hkueller/IoT_Anzeiger_V2/Network.cc

#include <Network.h>

network::network() {
	void *ptr;
	ptr=(WiFiServer *) malloc(sizeof(WiFiServer));
	server = (WiFiServer *) new(ptr) WiFiServer(80);
	ptr=(PubSubClient *) malloc(sizeof(PubSubClient));
	mqtt = (PubSubClient *) new(ptr) PubSubClient(mqtt_client);
}

void network::begin() {
	int retry=200;
	int zahl=0;
	clientId = "display_";

	//wifimanager.resetSettings();
	wifimanager.setConfigPortalTimeout(300);
#ifdef DEBUG
	Serial.println("Connecting WLAN");
	Serial.flush();
#endif
	if( ! wifimanager.autoConnect("IOTAnzeiger") ) {
#ifdef DEBUG
		Serial.println("Connecting to WLAN failed");
		Serial.println("Resetting the device");
		Serial.flush();
#endif
		ESP.restart();
	}
	ArduinoOTA.onStart([]() {
		String type;
		if (ArduinoOTA.getCommand() == U_FLASH) {
			type = "sketch";
		} else { // U_FS
			type = "filesystem";
		}
	});
#ifdef DEBUG
	Serial.println("Trying to get time from network");
	Serial.flush();
#endif
	configTime(MY_TZ, MY_NTP_SERVER);
	while(!getLocalTime(&zeit)) {
		if ( zahl < retry ) {
#ifdef DEBUG
			Serial.println("Time still not available. retry: " + String(zahl));
			Serial.flush();
#endif
			delay(100);
			zahl++;
		} else {
#ifdef DEBUG
			Serial.println("Timesetup failed");
			Serial.flush();
#endif
			break;
		}

	}
#ifdef DEBUG
	Serial.println("Initializing OTA");
	Serial.flush();
#endif
  	ArduinoOTA.begin();
#ifdef DEBUG
	Serial.println("Initializing WEB Server");
	Serial.flush();
#endif
	server->begin();
	server->setNoDelay(true);
#ifdef DEBUG
	Serial.println("Initializing MQTT Service");
	Serial.flush();
#endif
	mqtt->setServer(MQTT_SERVER,MQTT_PORT);
	mqtt->setCallback(mqtt_cb);
	clientId += String(random(0xffff), HEX);
#ifdef DEBUG
	Serial.print("Attempting MQTT connection...");
	Serial.flush();
#endif
	if (mqtt->connect(clientId.c_str())) {
#ifdef DEBUG
		Serial.print("connected, sending false to ");
		Serial.println(MQTT_REQUEST_TOPIC);
		Serial.flush();
#endif
		// Once connected, publish an announcement...
		mqtt->publish(MQTT_REQUEST_TOPIC, "false");
		// ... and resubscribe
#ifdef DEBUG
		Serial.print("subscribe ");
		Serial.println(MQTT_SUBSCRIBE_TOPIC);
		Serial.flush();
#endif
		mqtt->subscribe(MQTT_SUBSCRIBE_TOPIC);
#ifdef DEBUG
		Serial.println("mqtt setup ready");
		Serial.flush();
#endif
	}
#ifdef DEBUG
	Serial.println("Connecting to FHEM Instance");
	Serial.flush();
#endif
	network::FhemConnect();
	yield();
#ifdef DEBUG
	Serial.println("NETWORK SETUP FINISHED");
	Serial.flush();
#endif
	lastconfig=millis() + 1000*60;
}

int network::testNet(display *disp, smarthome *config) {
	int rc=0;
	int wifi_retry = 0;
	String reconmes="";
/*#ifdef DEBUG
	Serial.println("testNet() running");
	Serial.println("checking if WiFi is still connected");
	Serial.flush();
#endif*/
	while(WiFi.status() != WL_CONNECTED && wifi_retry < 15 ) {
#ifdef DEBUG
		Serial.println("Network Offline, Reconnect");
        	Serial.flush();
#endif
		reconmes="Try to Reconnect: ";
		reconmes+=wifi_retry;
		disp->Message("Network Offline!", reconmes, config);
		WiFi.disconnect();
		delay(100);
		wifimanager.setConfigPortalTimeout(300);
		wifimanager.autoConnect("IOTAnzeiger");
		delay(100);
		wifi_retry++;
		rc=1;
	}
	if(WiFi.status() != WL_CONNECTED) {
#ifdef DEBUG
		Serial.println("Network Offline, Reconnect failed, forcing system reset");
        	Serial.flush();
#endif
		disp->Message("Network Offline", "Rebooting", config);
		ESP.restart();
	}
	if((WiFi.status() == WL_CONNECTED) && ( rc == 1) ) {
		disp->Message("Network Reconnected","Setting up Network Services", config);
#ifdef DEBUG
		Serial.println("Cleaning up FhemConnection");
		Serial.flush();
#endif
		if(fhemclient) {
			FhemDisconnect();
		}
#ifdef DEBUG
		Serial.println("Checking for OTA");
        	Serial.flush();
#endif
  		ArduinoOTA.begin();
#ifdef DEBUG
		Serial.println("Pull System time with ntp");
        	Serial.flush();
#endif
		configTime(MY_TZ, MY_NTP_SERVER);
#ifdef DEBUG
		Serial.println("starting the servers");
        	Serial.flush();
#endif
		server->begin();
		server->setNoDelay(true);
		if (mqtt->connect(clientId.c_str())) {
#ifdef DEBUG
			Serial.print("connected, sending false to ");
			Serial.println(MQTT_REQUEST_TOPIC);
			Serial.flush();
#endif
			// Once connected, publish an announcement...
			mqtt->publish(MQTT_REQUEST_TOPIC, "false");
			// ... and resubscribe
#ifdef DEBUG
			Serial.print("subscribe ");
			Serial.println(MQTT_SUBSCRIBE_TOPIC);
			Serial.flush();
#endif
			mqtt->subscribe(MQTT_SUBSCRIBE_TOPIC);
#ifdef DEBUG
			Serial.println("mqtt setup ready");
			Serial.flush();
#endif
		}
		network::FhemConnect();
		network::mqttConnect();
		yield();
	}
	return(rc);
}

void network::handleWeb(smarthome *data) {
	//some variables
	//here for the actual client connection
	WiFiClient webclient;
	//and a buffer used to build the 
	//buffer to store the data send bei the client

	//Let us show if some client 
	//is available
	webclient = server->accept();
	if (webclient) {
		//do this only if we have a client
		String currentline = "";
		while(webclient.connected()) {
			//and if the client connection was successfull
			if (webclient.available()) {
				//and the client is still there
				//first of all we must take the initial GET call
				//of the client anywhere (http protocoll definition)
				//so let us read the send string char by char
				char c = webclient.read();
				header +=c;
				if ( c == '\n' ) {
					//OK we recived the newline command
					if (currentline.length() == 0 ) {
						//and nothing else - it was just a 
						//empty line -> we are ready to send our data

						//define a string to convert our
						//float values to stings
						String temp;
						//Let us load the web page into the temp string
						//start with HTML Header Information
						temp="HTTP/1.1 200 OK\n";
						temp+="Content-type:text/html\n";
						temp+="Connection: close\n\n";
						temp+="<!DOCTYPE HTML PUBLIC \"-//W3C//DTD HTML 4.0 Transitional//EN\">\n";
						temp+="<html><head><meta http-equiv=\"refresh\" content=\"60\"></head><body>\n";
						//stylesheed for a better table display
						temp+="<style>\ntable {\nborder-collapse: seperate;\nborder-spacing: 0.2em;\n}\ntbody tr:nth-child(even) td {\nbackground-color: #e4ebf2;\ncolor: #000;\n}\n\n";
						temp+="</style>\n\n";
						//start with the HTML HEader Information
						//display a Head Line and add some empty lines
						temp+="<H1><center>IOT Display Device</center>\n";
						temp+="</H1><br><br><center><table border=0 cellpadding=\"8\" cellspacing=\"0\" width=\"80%\"><tbody>\n";
						//get the information for the last data update
						temp+="<tr><td>Last Update:</td><td style=\"text-align:right\">\n";
						temp+=twodigit(zeit.tm_mday);
						temp+=".";
						temp+=twodigit(zeit.tm_mon+1);
						temp+=".";
						temp+=zeit.tm_year+1900;
						temp+=" ";
						temp+=twodigit(zeit.tm_hour);
						temp+=":";
						temp+=twodigit(zeit.tm_min);
						temp+=".";
						temp+=twodigit(zeit.tm_sec);
						if(data->SetFirst()) {
							if ( ! data->IsHeadline() ) {
								temp+="</td></tr><tr><td>";
								temp+=data->GetName();
								temp+=":</td><td style=\"text-align:right\">\n";
								temp+=data->GetData();
							}
							while(data->SetNext()) {
								if ( ! data->IsHeadline() ) {
									temp+="</td></tr><tr><td>";
									temp+=data->GetName();
									temp+=":</td><td style=\"text-align:right\">\n";
									temp+=data->GetData();
									temp+=" ";
									temp+=data->GetEinheit();
								}
							}
						}
						temp+="</td></tr></tbody></table></center><br></body></html>\n\n";
						//now send the string buffer
						webclient.print(temp);
						//and jump out -> we are ready and will close the connection
						break;
					} else {
						//this was not a empty line - so we have still to get data
						//empty the variable, and startover for the next line
						currentline = "";
					}
				} else if ( c != '\r' ) {
					//collect the line send by client char for char.
					currentline += c;
				}
			}
		}
		//reset our header variable
		header = "";
		// and stop the client connection
		webclient.flush();
		webclient.stop();
	}
	//give ESP8266 time to to wlan stuff
	yield();
}


int network::FhemConnect() {
	int conntry=0;

	if ( !fhemclient ) {
		void *ptr;
		ptr=(WiFiClient *) malloc(sizeof(WiFiClient));
		fhemclient = (WiFiClient *) new(ptr) WiFiClient();
		if(!fhemclient) {
			return 1;
		}
	}

	while ( ! fhemclient->connected() ) {
		if (!fhemclient->connect(FHEM_HOST, FHEM_PORT)) {
			yield();
			delay(100);
		}
		conntry++;
		if(conntry > 10) {
			return 1;
		}
	}
	return 0;
}

void network::FhemDisconnect() {
	if(fhemclient) {
		fhemclient->flush();
		fhemclient->stop();
		delete(fhemclient);
		fhemclient=0;
	}
}

int network::FhemConnCheck() {
	int connectry=0;
	while( FhemConnect() == 1 ) {
#ifdef DEBUG
		Serial.println("Try to reconnect FHEM");
#endif
		if(connectry > 10 ) {
			break;
		}
		yield();
		delay(100);
		connectry++;
		if (connectry > 10) {
			return 1;
		}
	}
	return 0;
}

void network::UpdateData(display *disp, smarthome *data) {
	String Result;

	if(FhemConnCheck() == 1) { return; };
#ifdef DEBUG
	Serial.println("FHEM Connection OK\n");
        Serial.flush();
        Serial.flush();
#endif
	fhemclient->print("\n");
	while(fhemclient->available()) {
		Result = fhemclient->readStringUntil('\n');
	}
	fhemclient->flush();
#ifdef DEBUG
	Serial.println("Start reading data");
        Serial.flush();
#endif
	if(data->SetFirst()) {
		if ( ! data->IsHeadline() ) {
			for ( int i=0; i<FHEM_RETRY; i++) {
#ifdef DEBUG
				Serial.println(data->GetDev() + "->" + data->GetReading() );
				Serial.flush();
#endif
				if(FhemConnCheck() == 1) { return; };
				if (FhemGetData(&Result, data->GetDev(), data->GetReading()) == 1 ) {
					data->SetData(Result);
					break;
				} else {
					Result="-1";
					data->SetData(Result);
				}
			}
		}
		while(data->SetNext()) {
			for ( int i=0; i<FHEM_RETRY; i++) {
#ifdef DEBUG
				Serial.println(data->GetDev() + "->" + data->GetReading() );
				Serial.flush();
#endif
				if(FhemConnCheck() == 1) { return; };
				if (FhemGetData(&Result, data->GetDev(), data->GetReading()) == 1 ) {
					data->SetData(Result);
					break;
				} else {
					Result="-1";
					data->SetData(Result);
				}
			}
		}
#ifdef DEBUG
		Serial.println("Updateing Timer");
        	Serial.flush();
#endif
		StoreTimeLastRead();
		Result=twodigit(zeit.tm_mday);
		Result+=".";
		Result+=twodigit(zeit.tm_mon+1);
		Result+=" ";
		Result+=twodigit(zeit.tm_hour);
		Result+=":";
		Result+=twodigit(zeit.tm_min);
		disp->SetDate(Result);
		disp->EnableUpdate();
		/*
#ifdef DEBUG
		Serial.println("Clearing fhem read buffer");
        	Serial.flush();
#endif
		while(fhemclient->available()) {
			fhemclient->flush();
			yield();
		}*/
#ifdef DEBUG
		Serial.println("quitting fhem");
        	Serial.flush();
#endif
		fhemclient->print("quit\n");
	} else {
		RequestConfig();
		fhemclient->print("quit\n");
	}
#ifdef DEBUG
	Serial.println("Reading data completed");
	Serial.flush();
#endif
};

int network::FhemGetData(String *result, const String device, const String reading) {
	String buffer;
	int pos;
	int readwait=0;

	*result="";
#ifdef DEBUG
	Serial.println("Flushing Network input");
       	Serial.flush();
#endif
	while(fhemclient->available()) {
		buffer = fhemclient->read();
	}
	buffer = "{ ReadingsVal(\"" + device + "\",\"" + reading + "\",0) }\n";
#ifdef DEBUG
	Serial.println("Send fhem command");
       	Serial.flush();
#endif
	fhemclient->print(buffer);
#ifdef DEBUG
	Serial.println("Waiting for answer");
       	Serial.flush();
#endif
	readwait=0;
	while(fhemclient->available() < 1 ) {
		yield();
		delay(100);
		readwait++;
		if ( readwait > 50 ) {
			break;
		}
	}
#ifdef DEBUG
	Serial.println("Reading answer");
       	Serial.flush();
#endif
	*result=fhemclient->readStringUntil('\n');
	result->trim();
	pos=result->indexOf("fhem>");
	if(pos > -1) {
		*result=result->substring(pos+5);
	}
#ifdef DEBUG
	Serial.println("done");
       	Serial.flush();
#endif
	return(1);
}

void network::handleOTA() {
	ArduinoOTA.handle();
}

void network::handleNet(smarthome *sm, display *disp) {
/*#ifdef DEBUG
	Serial.println("Running mqtt loop");
	Serial.flush();
#endif*/
	if(mqtt->connected()) {
		mqtt->loop();
	} else {
		network::mqttConnect();
	}
	yield();
/*#ifdef DEBUG
	Serial.println("Running OTA");
	Serial.flush();
#endif*/
	ArduinoOTA.handle();
	yield();
	if ( millis() - disp->getLastTime() > UPDATE_MINUTE * 1000 * 60) {
#ifdef DEBUG
		Serial.println("Updating smarthome Data");
		Serial.flush();
#endif
		UpdateData(disp,sm);
		yield();
	}
/*#ifdef DEBUG
	Serial.println("Running WEB");
#endif*/
	handleWeb(sm);
	yield();
/*#ifdef DEBUG
	Serial.print("millies: ");
	Serial.print(millis());
	Serial.print(" lasttime: ");
	Serial.println(lastconfig);
#endif*/
	if ( millis() > (lastconfig + (1000*600)) ) {
#ifdef DEBUG
		Serial.println("Requesting Config");
#endif
		RequestConfig();
		lastconfig=millis();
	}
}

void network::StoreTimeLastRead() {
        time_t now;

        now = time(nullptr);
        localtime_r(&now, &zeit);
}

int network::ReturnYear() {
	return(zeit.tm_year+1990);
}

int network::ReturnMonth() {
	return(zeit.tm_mon);
}

int network::ReturnDay() {
	return(zeit.tm_mday);
}

int network::ReturnHour() {
	return(zeit.tm_hour);
}

int network::ReturnMinutes() {
	return(zeit.tm_min);
}

String network::ReturnSeconds() {
	String seconds;

	if ( zeit.tm_sec < 0 ) {
		seconds=0;
		seconds+=zeit.tm_sec;
	} else {
		seconds=zeit.tm_sec;
	}
	return(seconds);
}

String network::twodigit(int number) {
	String buffer;

	buffer="";
	if ( number < 10 ) {
		buffer+="0";
	}
	buffer+=number;
	return(buffer);
}

void network::RequestConfig() {
	mqtt->publish(MQTT_REQUEST_TOPIC,"true");
}

void network::ConfigDone() {
	mqtt->publish(MQTT_REQUEST_TOPIC,"false");
}

void network::mqttConnect() {
	Serial.print("Attempting MQTT connection...");
	// Create a random client ID
	// Attempt to connect
	mqtt->setServer(MQTT_SERVER,MQTT_PORT);
	//mqtt->setCallback(callback);
	mqtt->setCallback(mqtt_cb);
	clientId += String(random(0xffff), HEX);
#ifdef DEBUG
	Serial.print("Attempting MQTT connection...");
	Serial.flush();
#endif
	if (mqtt->connect(clientId.c_str())) {
		Serial.println("connected");
		// Once connected, publish an announcement...
		mqtt->publish(MQTT_REQUEST_TOPIC, "false");
		// ... and resubscribe
		mqtt->subscribe(MQTT_SUBSCRIBE_TOPIC);
	} else {
		Serial.print("failed, rc=");
		Serial.print(mqtt->state());
		Serial.println(" try again in 5 seconds");
		// Wait 5 seconds before retrying
		delay(5000);
	}
}
