hkueller/IoT_Anzeiger_V2/Network.h

#ifndef __NETWORK_H
#define __NETWORK_H

#if defined(ARDUINO_ARCH_ESP32)
#include <Arduino.h>
#include <WiFi.h>
//#include <ESPAsyncWebServer.h>
//#include <AsyncTCP.h>
#endif

#if defined(ARDUINO_ARCH_ESP8266)
#include <ESP8266WiFi.h>
#endif

#include <DNSServer.h>

#include <WiFiManager.h>
#include <WiFiUdp.h>
#include <ArduinoOTA.h>
#include <Display.h>
#include <time.h>
#include "sntp.h"
#include <PubSubClient.h>
#include <config.h>
#include <Data.h>
#ifdef USE_WEBSERIAL
#include <webSerial.h>
#endif

//void callback(char* topic, byte* payload, unsigned int length);
void mqtt_cb(char* topic, byte* payload, unsigned int length);

class network {
private:
	String header;
	String clientId;
	tm zeit;

	WiFiManager wifimanager;
	WiFiServer *server;
	WiFiClient *fhemclient=0;
	WiFiClient mqtt_client;
	void mqttConnect();
	PubSubClient *mqtt;
public:
	network();
	void begin();
	int testNet(display *disp, smarthome *config);
	void handleWeb(smarthome *data);
	void UpdateData(display *disp, smarthome *data);
	//int FhemGetData(String *result,const String device, const String reading, long unsigned int *lasttime);
	int FhemGetData(String *result,const String device, const String reading);
	//WiFiClient * FhemConnect();
	int FhemConnect();
	void FhemDisconnect();
	int FhemConnCheck();
	void handleOTA();
	void handleNet(smarthome *sm, display *disp);
	void StoreTimeLastRead();
	String twodigit(int number);
	int ReturnYear();
	int ReturnMonth();
	int ReturnDay();
	int ReturnHour();
	int ReturnMinutes();
	String ReturnSeconds();
	void RequestConfig();
	void ConfigDone();
	//long unsigned int lasttime=0;
	long unsigned int lastconfig=0;

};
#endif
